d3athstr/mesh-internet-gateway/hardware/meshgw-hat/out/fab/meshgw-fab-preview.png

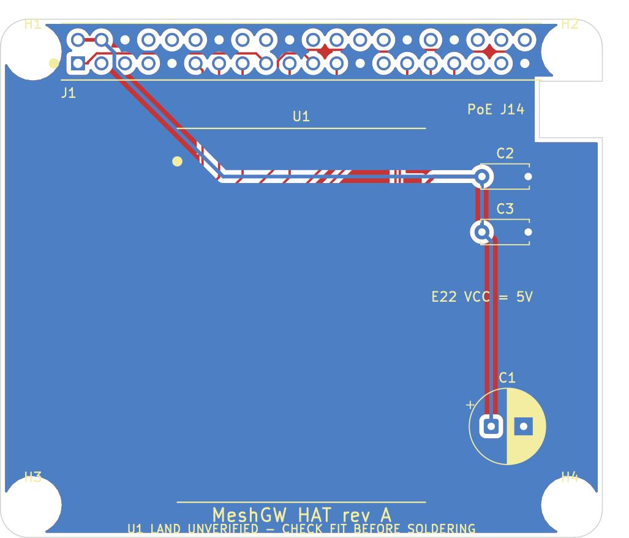
hardware/meshgw-hat/out/fab/meshgw-fab-preview.png
